ZigbeeLink/EFR32_version/Images/Case2.jpg

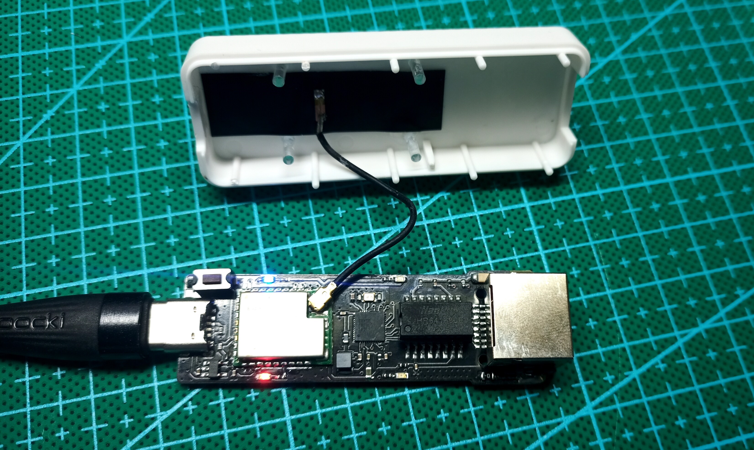
Images/Case2.jpg
